mooped/m-link-lite/main/servo.h

#pragma once

/// Enable/disable all servos
void servo_enable(void);
void servo_disable(void);

// Set desired servo pulse width in ms
void servo_set(int channel, int pulsewidth_ms);

// Update all servos and refresh
void servo_set_all(int s1, int s2, int s3, int s4, int s5, int s6);

/// Initialise the PWM/servo control module
void servo_init(void);
