mooped/m-link-lite/main/rx-pwm.c

/* pwm example

   This example code is in the Public Domain (or CC0 licensed, at your option.)

   Unless required by applicable law or agreed to in writing, this
   software is distributed on an "AS IS" BASIS, WITHOUT WARRANTIES OR
   CONDITIONS OF ANY KIND, either express or implied.
*/

#include <stdio.h>
#include <string.h>
#include <stdlib.h>

#include "freertos/FreeRTOS.h"

#include "esp_log.h"
#include "esp_system.h"
#include "esp_err.h"

#include "esp8266/gpio_register.h"
#include "esp8266/pin_mux_register.h"

#include "driver/pwm.h"

#define PWM_IO_COUNT      6

#define PWM_0_OUT_IO_NUM  4   // Motor 1A
#define PWM_1_OUT_IO_NUM  5   // Motor 1B
#define PWM_2_OUT_IO_NUM  15  // Motor 2A
#define PWM_3_OUT_IO_NUM  13  // Motor 2B
#define PWM_4_OUT_IO_NUM  12  // Motor 3A
#define PWM_5_OUT_IO_NUM  14  // Motor 3B

#define PWM_M1A_CHANNEL 0
#define PWM_M1B_CHANNEL 1
#define PWM_M2A_CHANNEL 2
#define PWM_M2B_CHANNEL 3
#define PWM_M3A_CHANNEL 4
#define PWM_M3B_CHANNEL 5

// PWM period 1024us(~1Khz)
#define PWM_PERIOD    (511)

static const char *TAG = "m-link-rx-pwm";

// pwm pin number
const uint32_t pin_num[PWM_IO_COUNT] = {
  PWM_0_OUT_IO_NUM,
  PWM_1_OUT_IO_NUM,
  PWM_2_OUT_IO_NUM,
  PWM_3_OUT_IO_NUM,
  PWM_4_OUT_IO_NUM,
  PWM_5_OUT_IO_NUM,
};

// duties table, real_duty = duties[x]/PERIOD
uint32_t duties[PWM_IO_COUNT] = {
  0, 0, 0, 0, 0, 0,
};

// phase table, delay = (phase[x]/360)*PERIOD
float phase[PWM_IO_COUNT] = {
  0.f, 0.f, 0.f, 0.f, 0.f, 0.f,
};

void rx_pwm_init(void)
{
  ESP_ERROR_CHECK( pwm_init(PWM_PERIOD, duties, PWM_IO_COUNT, pin_num) );
  ESP_ERROR_CHECK( pwm_set_phases(phase) );
  ESP_ERROR_CHECK( pwm_start() );
}

void rx_pwm_set_motor(int speed, int channel_a, int channel_b)
{
  // Coast
  if (speed == 0)
  {
    duties[channel_a] = 0;
    duties[channel_b] = 0;
  }
  // Brake
  else if (speed == 512)
  {
    duties[channel_a] = PWM_PERIOD;
    duties[channel_b] = PWM_PERIOD;
  }
  // Drive
  else
  {
    // Coast when not driving
    if (speed > 0)
    {
      duties[channel_a] = 0;
      duties[channel_b] = (speed > 511) ? 511 : speed;
    }
    else
    {
      duties[channel_a] = (speed < -511) ? 511 : -speed;
      duties[channel_b] = 0;
    }
  }
}

void rx_pwm_set_motors(int m1, int m2, int m3)
{
  rx_pwm_set_motor(m1, PWM_M1A_CHANNEL, PWM_M1B_CHANNEL);
  rx_pwm_set_motor(m2, PWM_M2A_CHANNEL, PWM_M2B_CHANNEL);
  rx_pwm_set_motor(m3, PWM_M3A_CHANNEL, PWM_M3B_CHANNEL);
}

void rx_pwm_update(void)
{
  pwm_set_duties(duties);
  pwm_start();
}
